alexandre-pereira/trimming-tools/apercu/accrochage_dessus.png

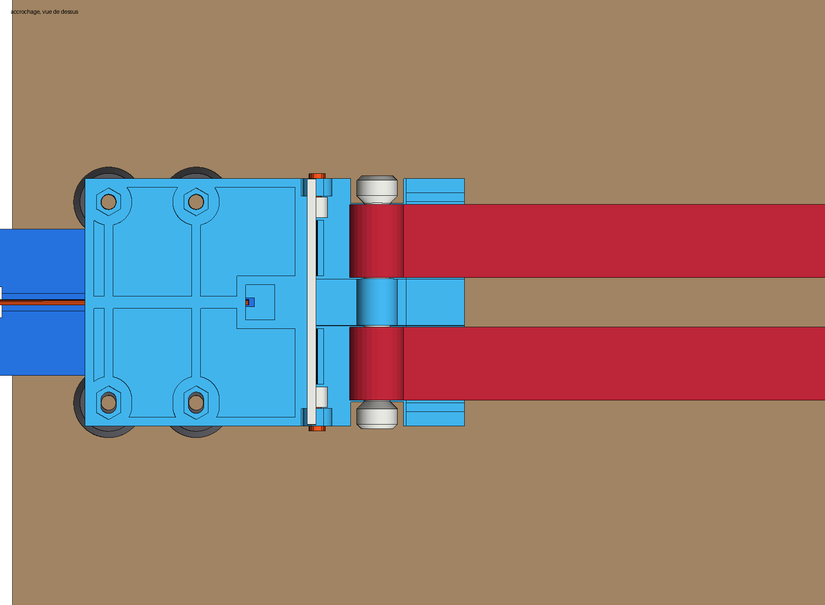
apercu/accrochage_dessus.png
