alexandre-pereira/trimming-tools/apercu/accrochage_profil.png

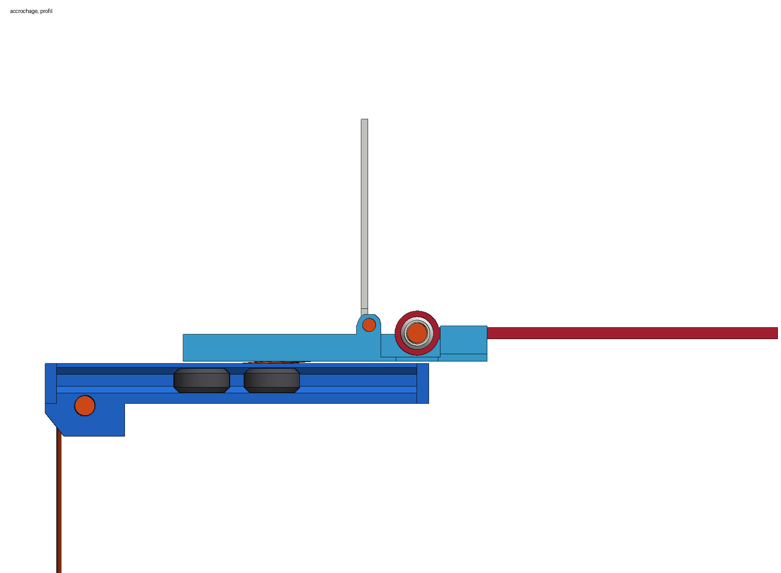
apercu/accrochage_profil.png
