alexandre-pereira/trimming-tools/apercu/banc_ouvert_arriere.png

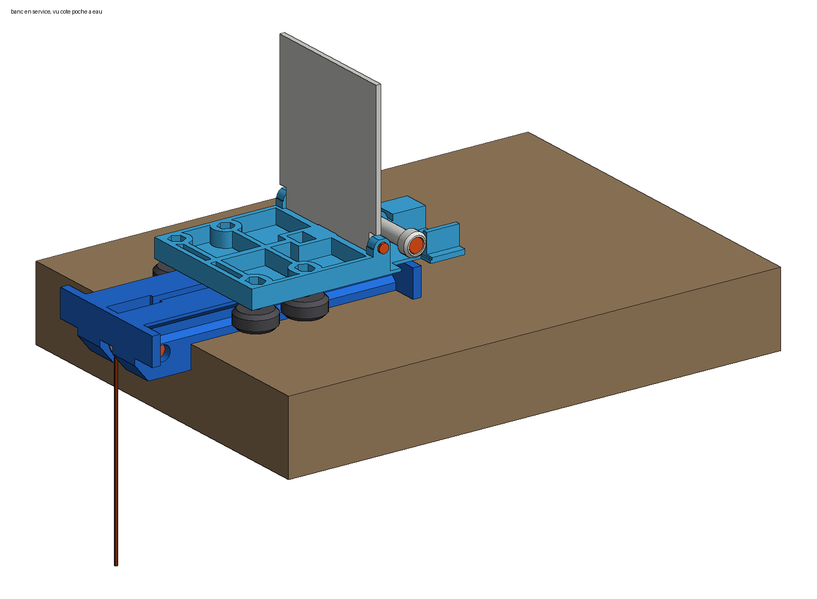
apercu/banc_ouvert_arriere.png
