alexandre-pereira/trimming-tools/apercu/banc_ouvert_profil.png

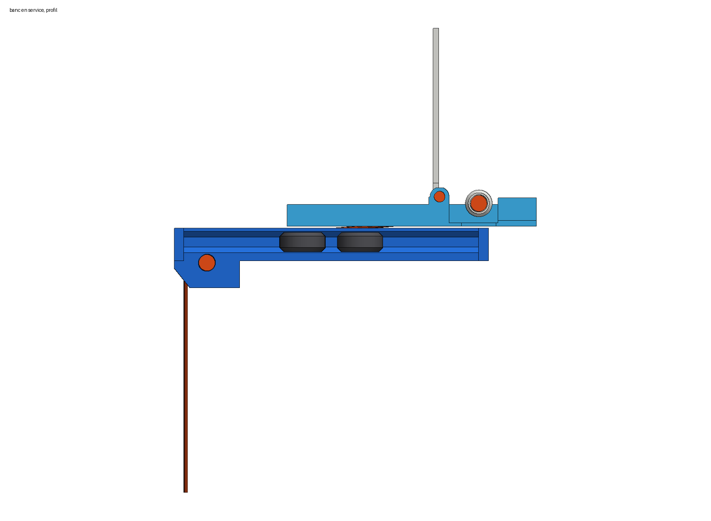
apercu/banc_ouvert_profil.png
