alexandre-pereira/trimming-tools/apercu/banc_plie_profil.png

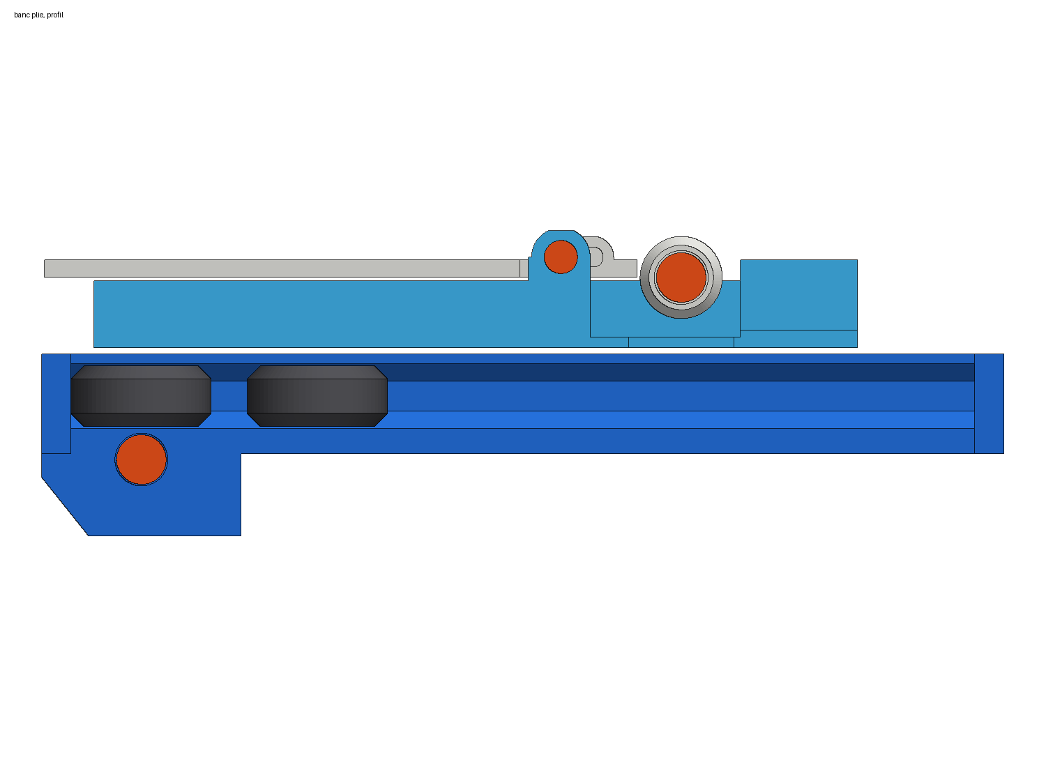
apercu/banc_plie_profil.png
