alexandre-pereira/trimming-tools/apercu/bobine_ecrou.png

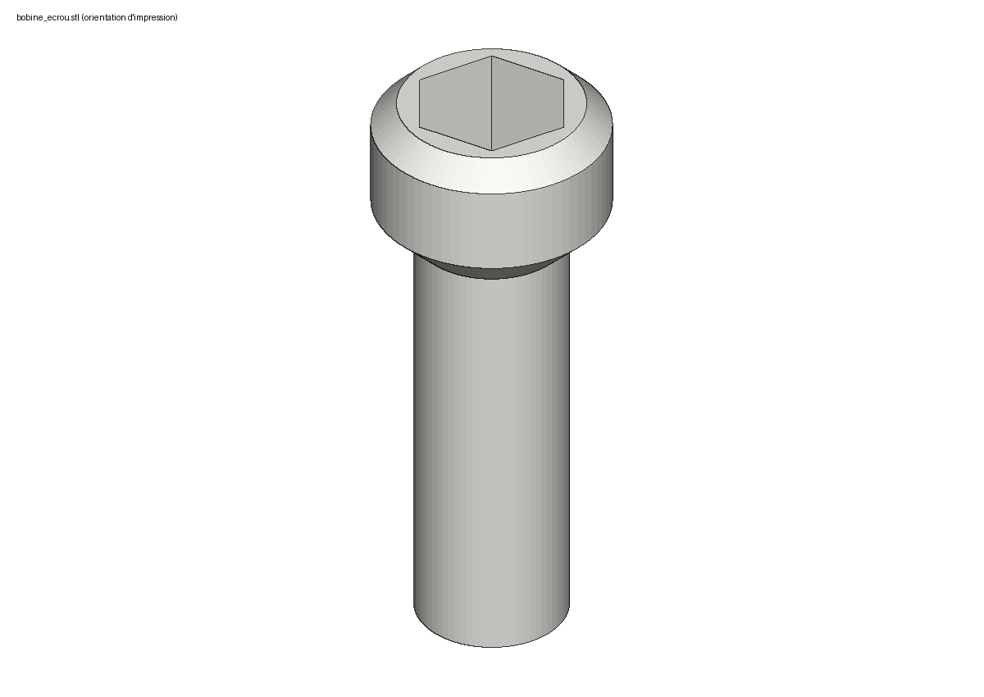
apercu/bobine_ecrou.png
