alexandre-pereira/trimming-tools/apercu/coulisseau.png

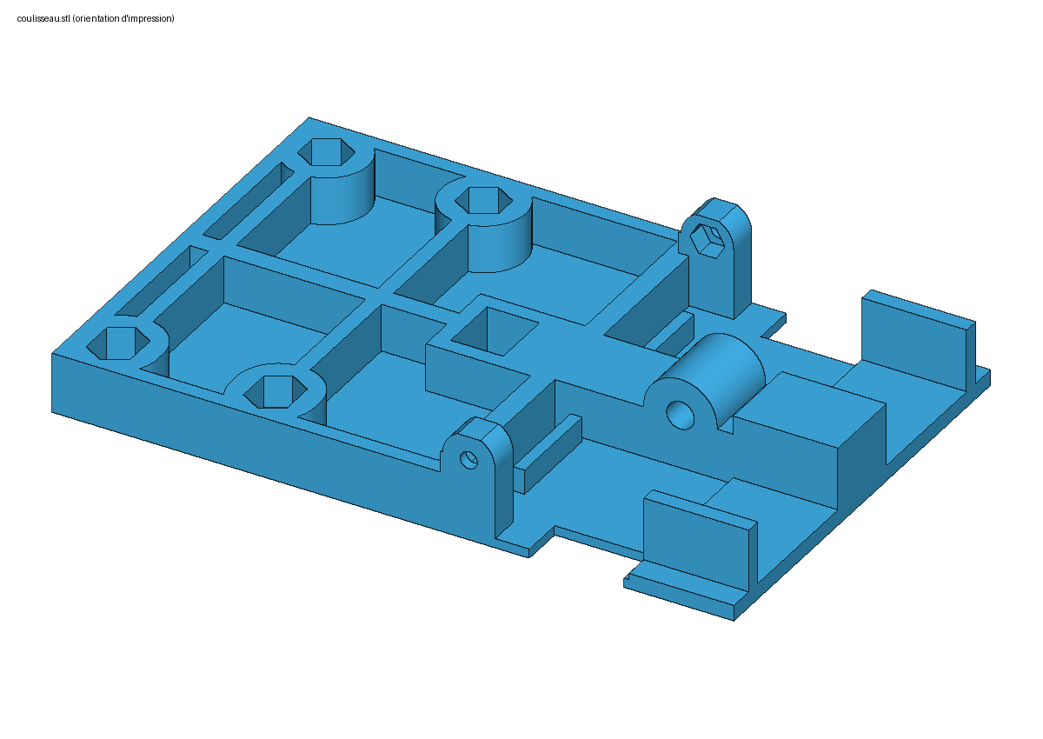
apercu/coulisseau.png
