alexandre-pereira/trimming-tools/apercu/poulie.png

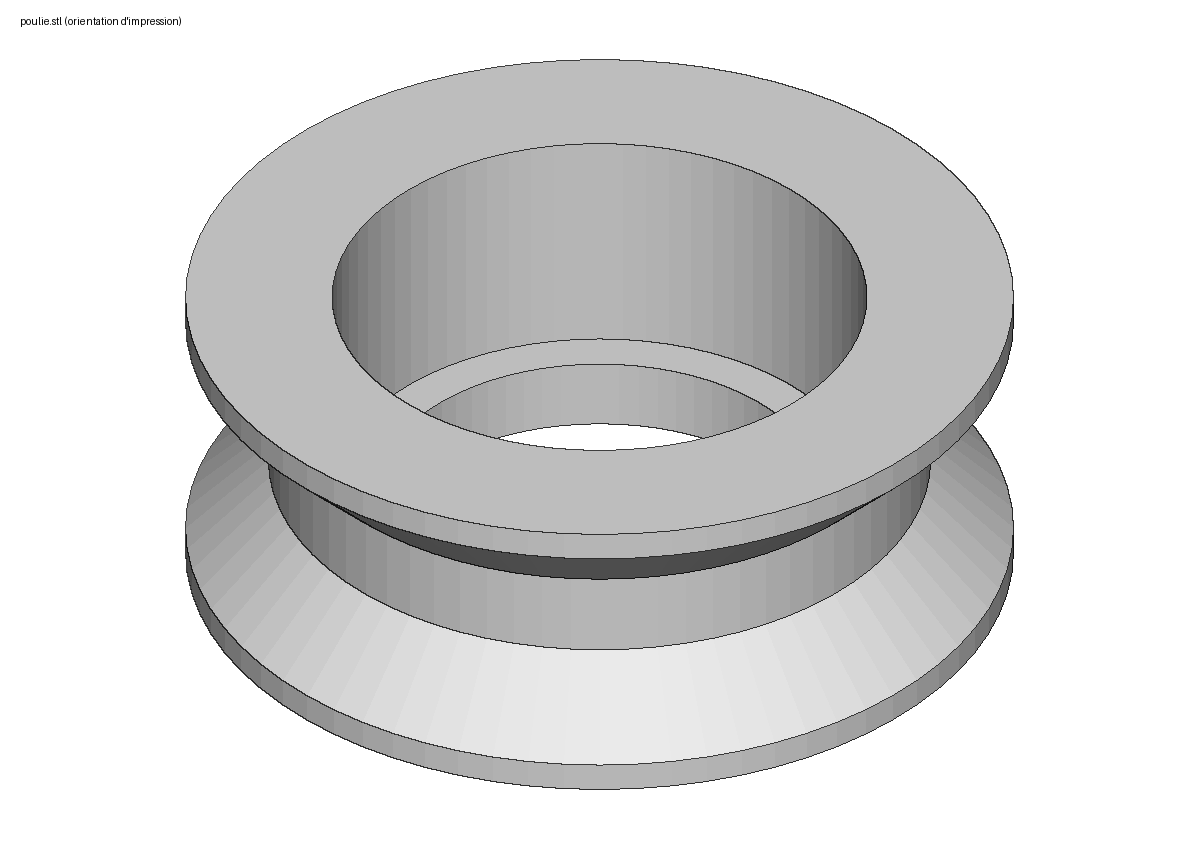
apercu/poulie.png
