alexandre-pereira/trimming-tools/apercu/schema_A_roue.png

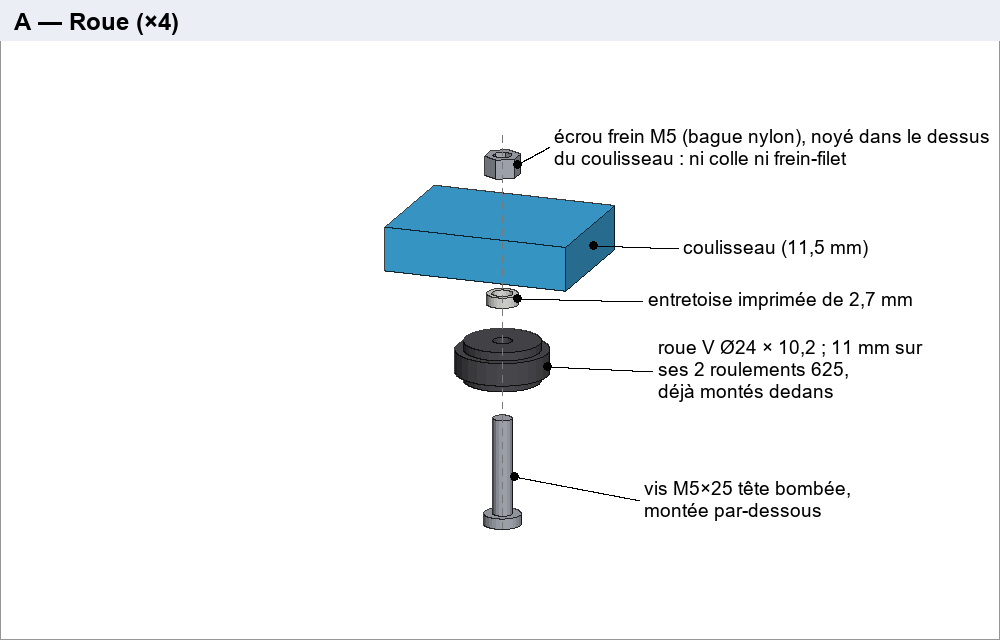
apercu/schema_A_roue.png
