alexandre-pereira/trimming-tools/apercu/schema_B_poulie.png

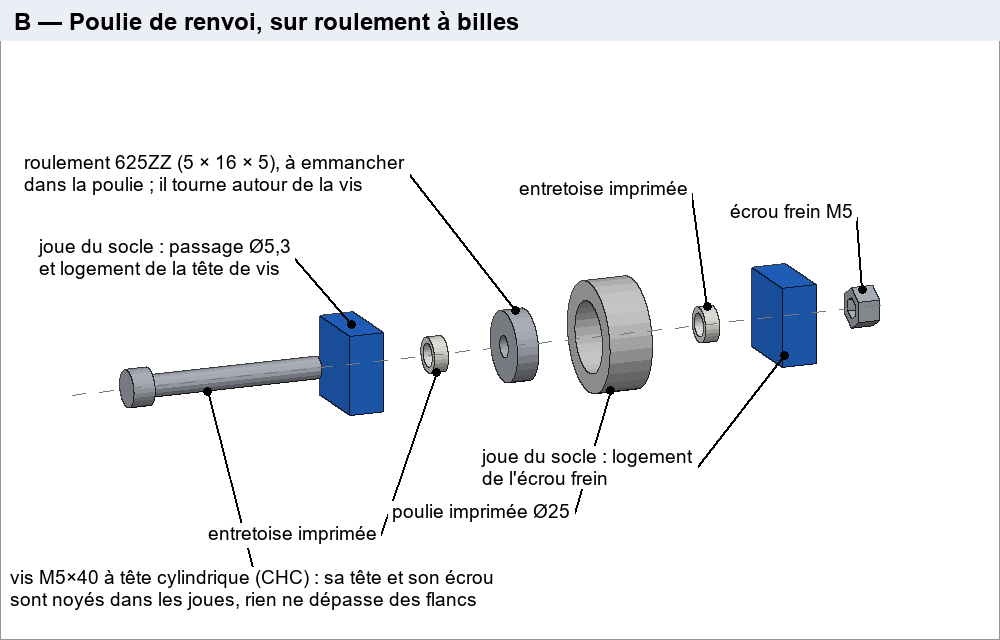
apercu/schema_B_poulie.png
