alexandre-pereira/trimming-tools/apercu/schema_C_axe_elevateurs.png

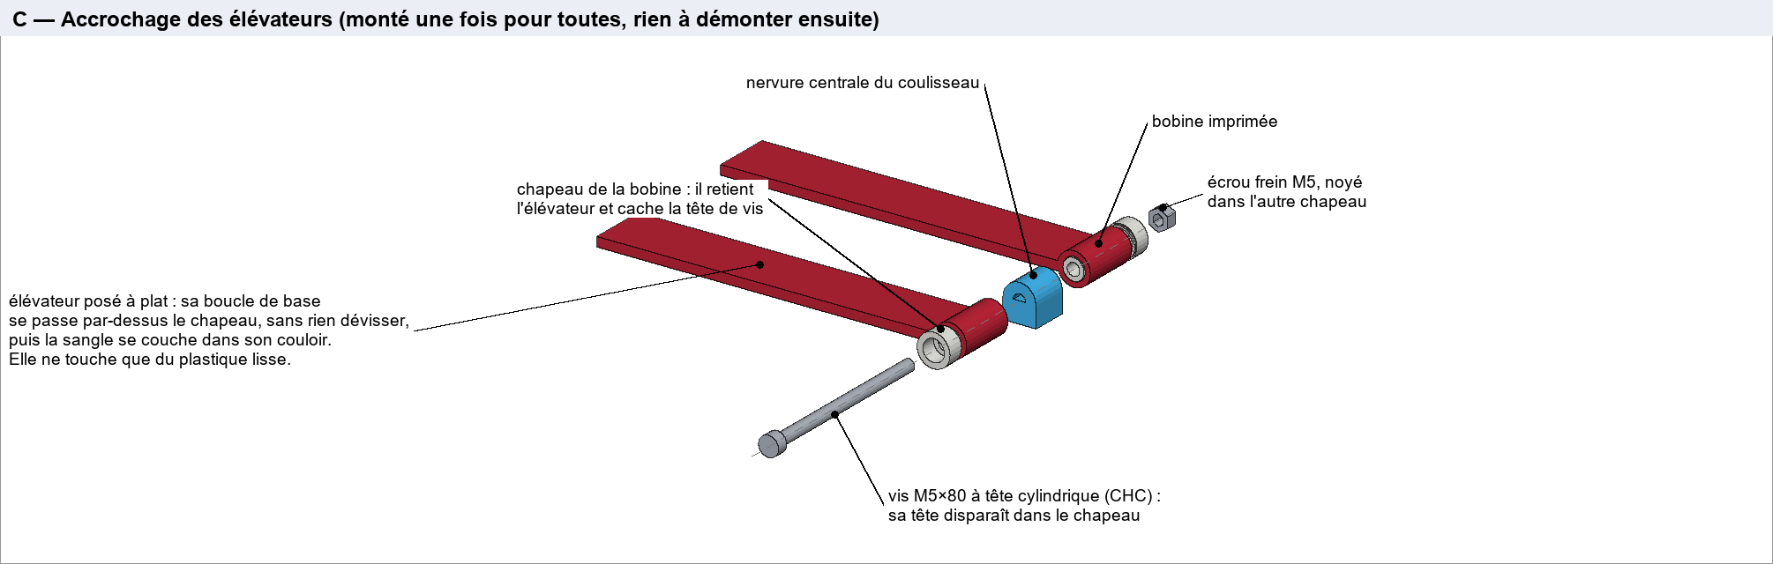
apercu/schema_C_axe_elevateurs.png
