alexandre-pereira/trimming-tools/apercu/schema_D_charniere.png

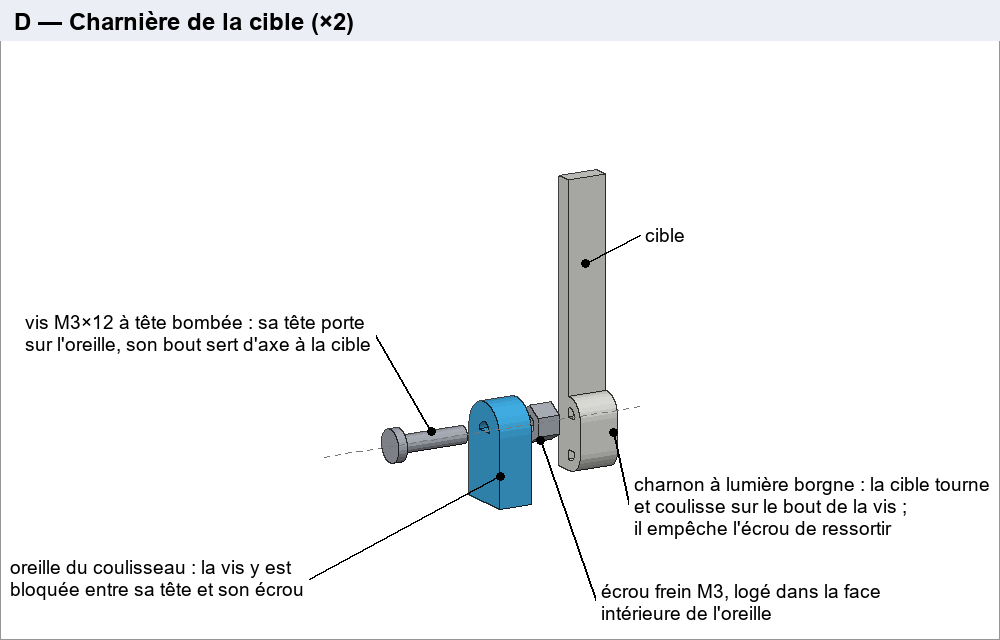
apercu/schema_D_charniere.png
