alexandre-pereira/trimming-tools/apercu/schema_E_cordelette.png

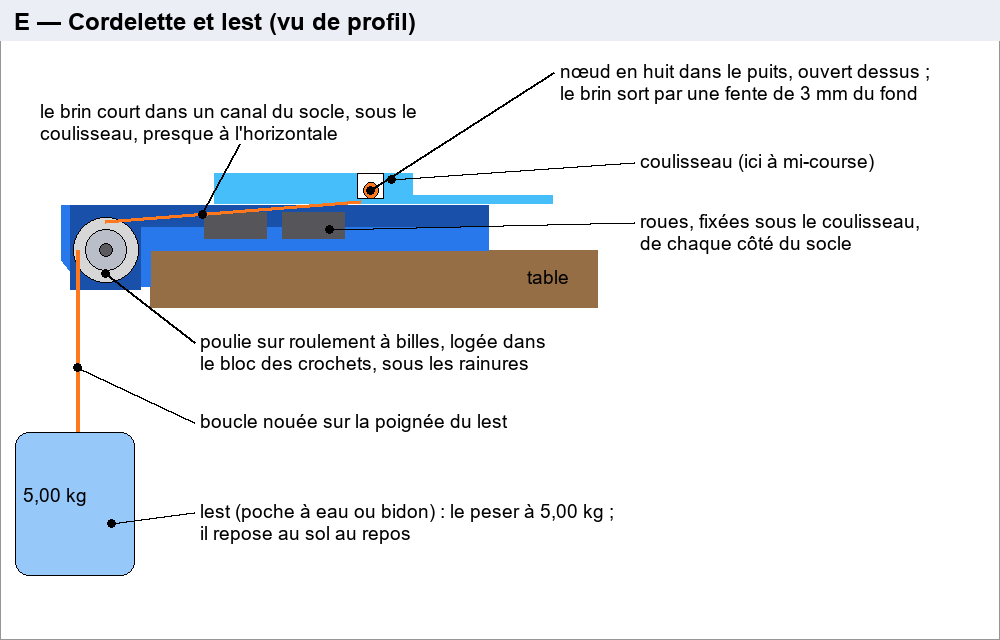
apercu/schema_E_cordelette.png
