alexandre-pereira/trimming-tools/apercu/schema_F_verrou_cible.png

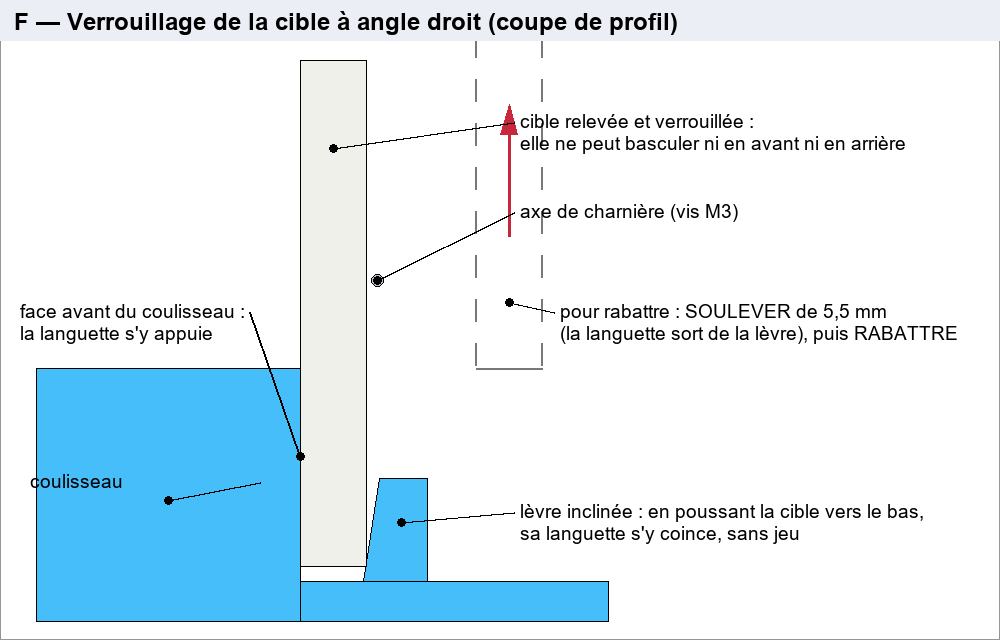
apercu/schema_F_verrou_cible.png
