alexandre-pereira/trimming-tools/apercu/support_laser_arriere.png

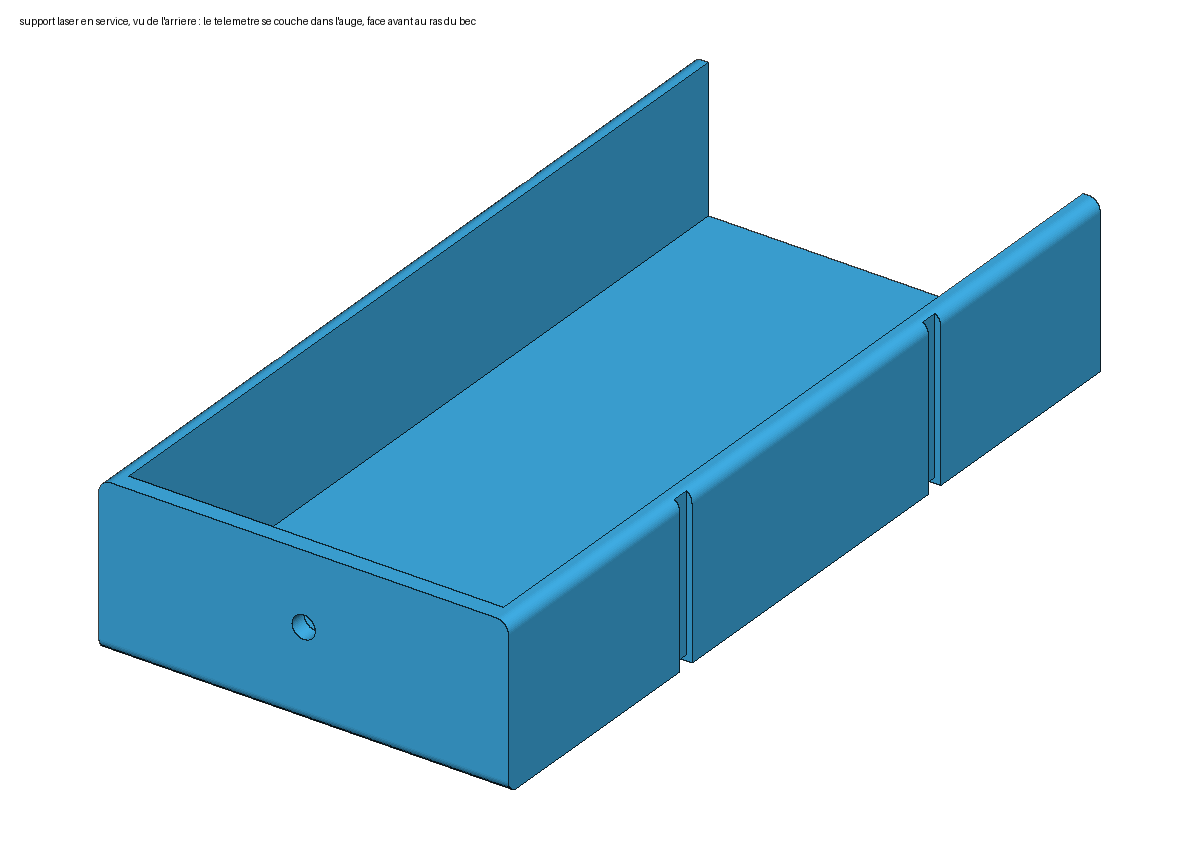
apercu/support_laser_arriere.png
