alexandre-pereira/trimming-tools/apercu/support_laser_bec.png

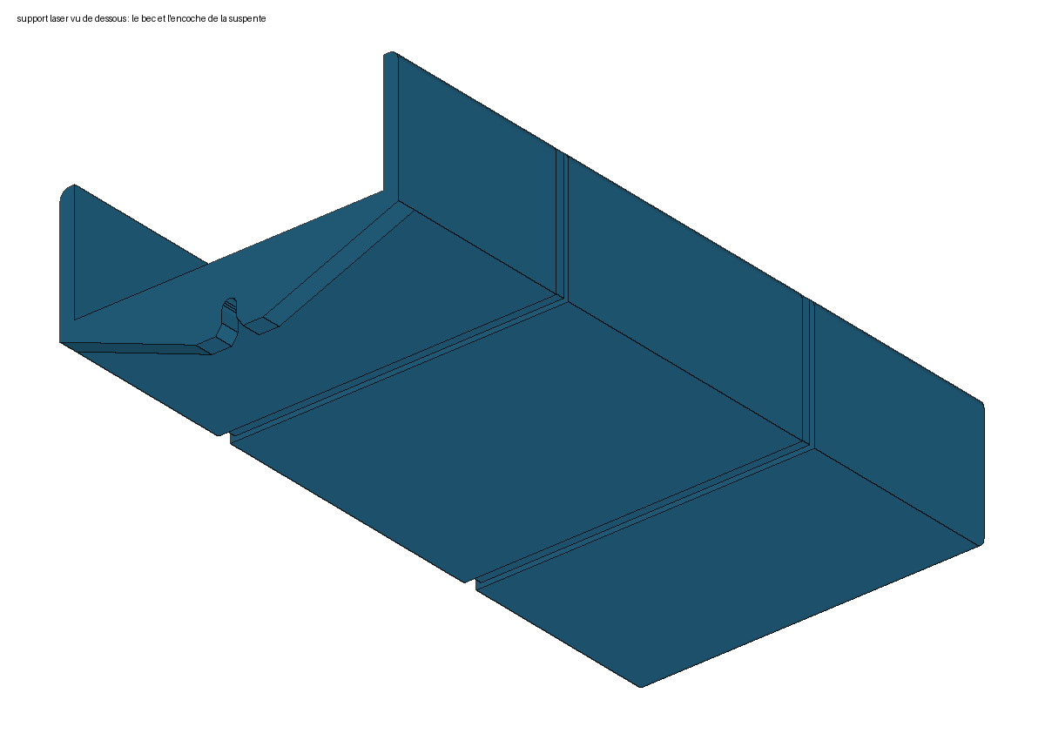
apercu/support_laser_bec.png
