alexandre-pereira/trimming-tools/stl/support_laser_bosch_glm50.stl

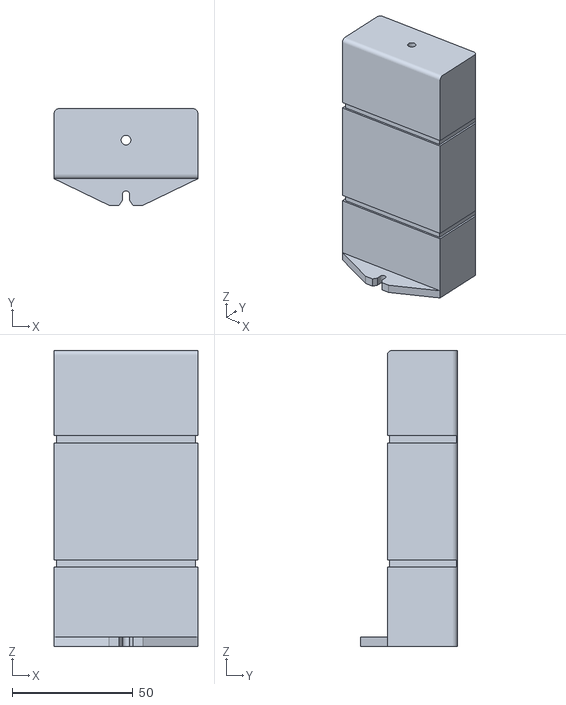
[picture p39: CAD file, 2026-10-07]
stl/support_laser_bosch_glm50.stl
59.5 x 40.0 x 122.5
