alexandre-pereira/trimming-tools/stl/support_laser_leica_d1.stl

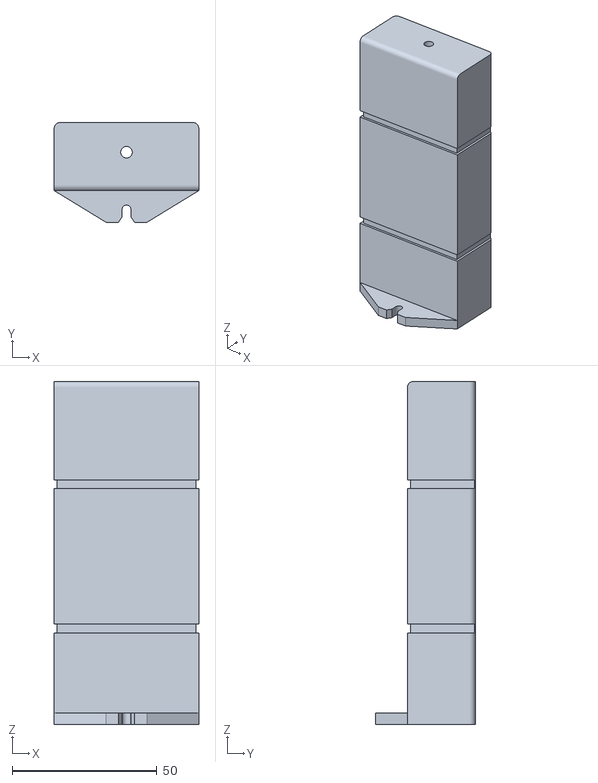
[picture p40: CAD file, 2026-10-07]
stl/support_laser_leica_d1.stl
50.0 x 34.5 x 118.5
