alexandre-pereira/trimming-tools/stl/bobine_ecrou.stl

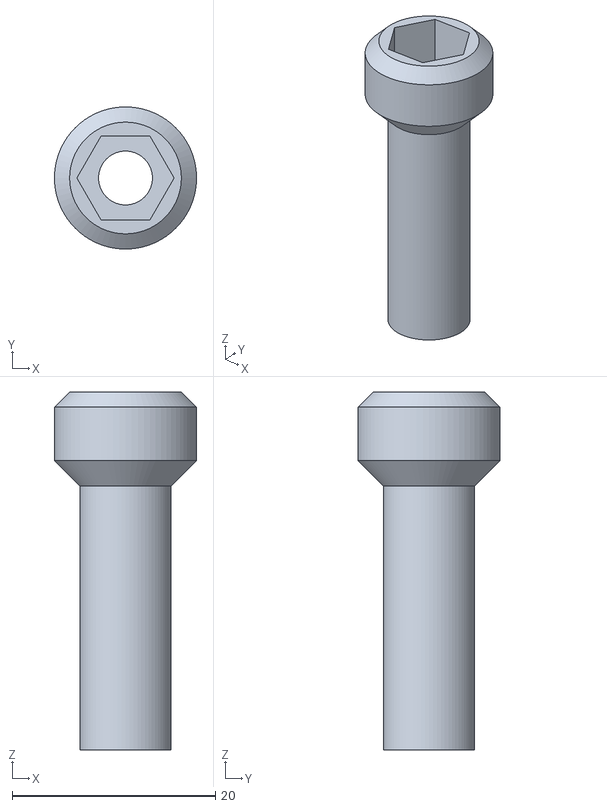
[picture p41: CAD file, 2026-10-07]
stl/bobine_ecrou.stl
14.0 x 14.0 x 35.2
