alexandre-pereira/trimming-tools/stl/cible.stl

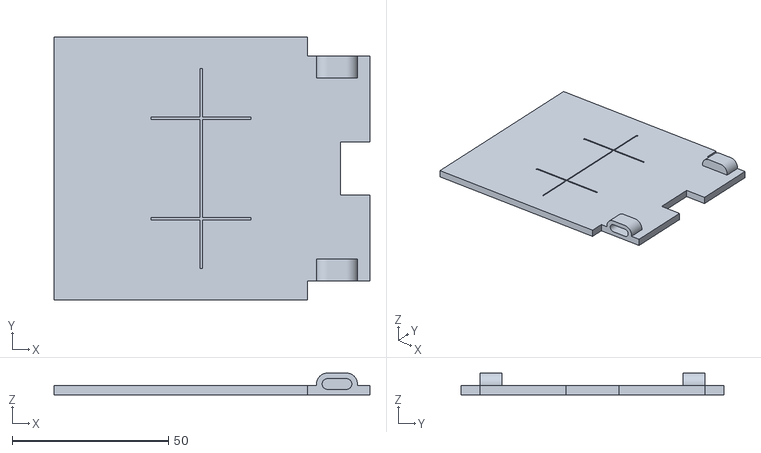
[picture p42: CAD file, 2026-10-07]
stl/cible.stl
101.0 x 84.0 x 7.00
