alexandre-pereira/trimming-tools/stl/poulie.stl

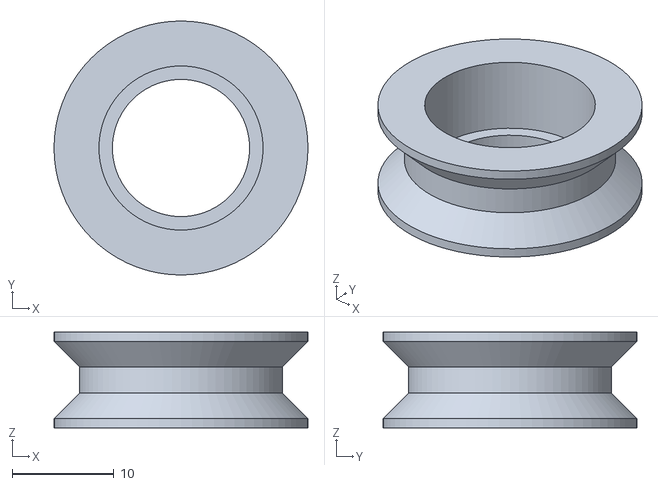
[picture p43: CAD file, 2026-10-07]
stl/poulie.stl
25.0 x 25.0 x 9.40
