alexandre-pereira/trimming-tools/stl/entretoises_grappe.stl

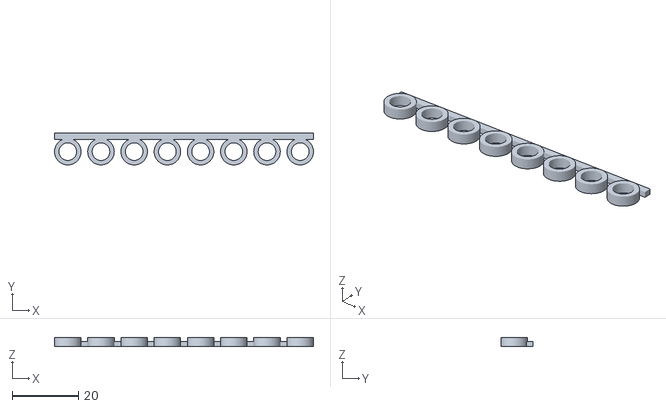
[picture p44: CAD file, 2026-10-07]
stl/entretoises_grappe.stl
78.0 x 9.60 x 2.70
