alexandre-pereira/trimming-tools/apercu/schema_montage.png

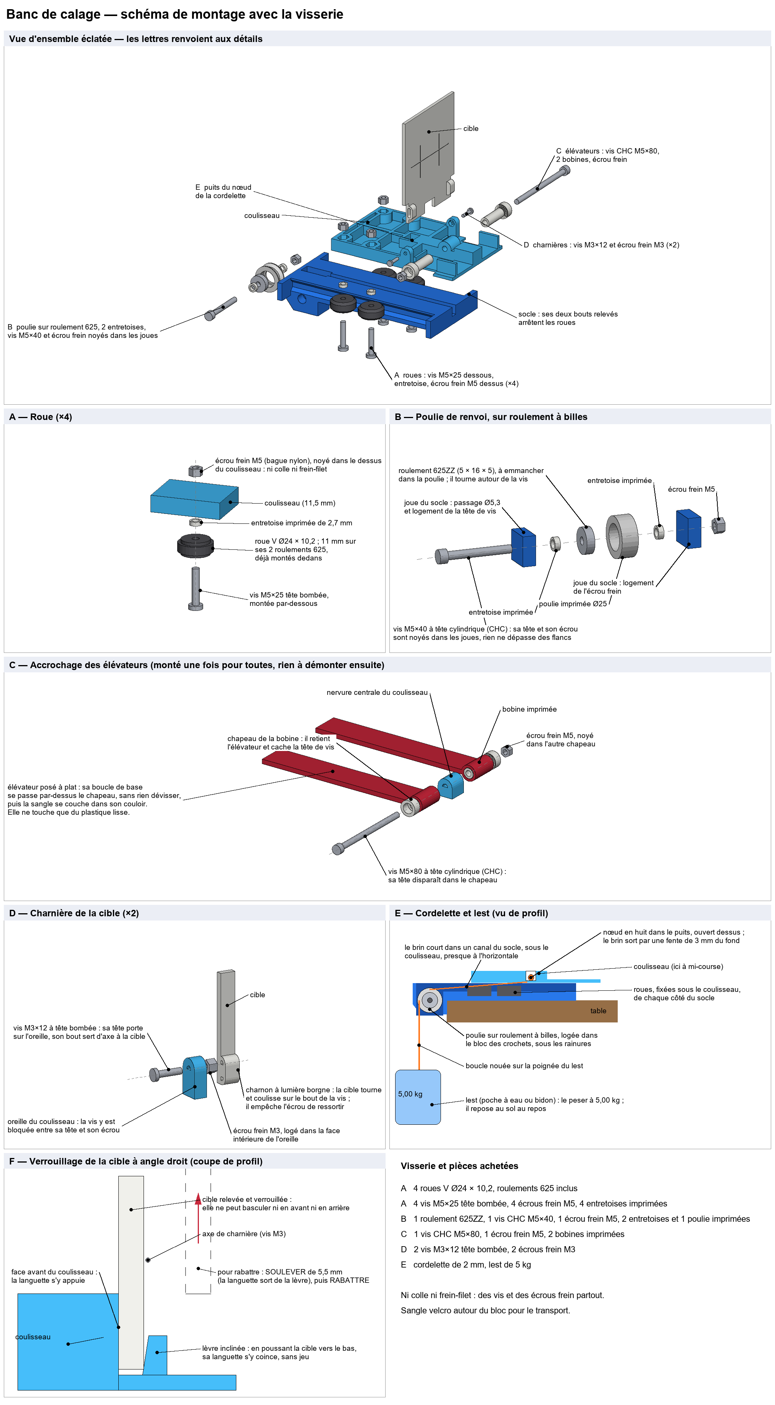
apercu/schema_montage.png
